TigerTag-Project/Tiger_Scale/data/www/img/bambu_grey.png

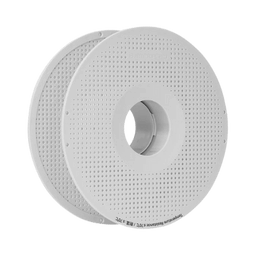
data/www/img/bambu_grey.png
