TigerTag-Project/Tiger_Scale/data/www/img/bambu_transp.png

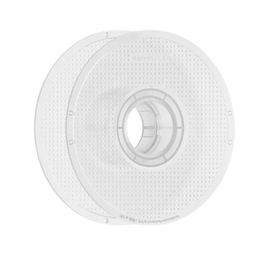
data/www/img/bambu_transp.png
