TigerTag-Project/Tiger_Scale/data/www/img/custom.png

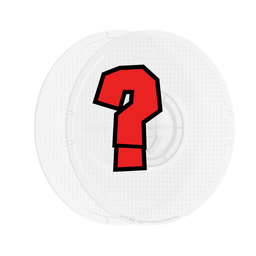
data/www/img/custom.png
