TigerTag-Project/Tiger_Scale/data/www/img/r3d_grey.png

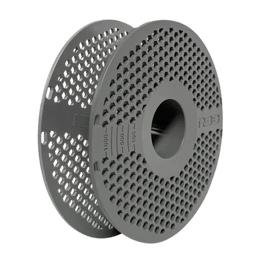
data/www/img/r3d_grey.png
