TigerTag-Project/Tiger_Scale/hardware/photo/1.jpg

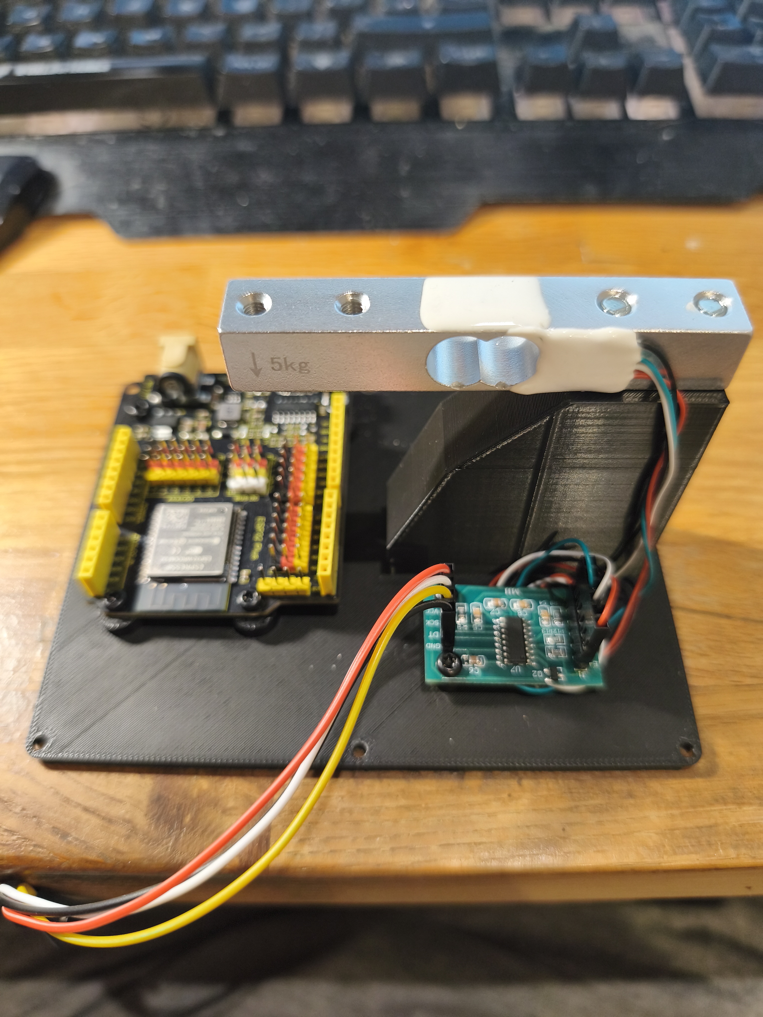
hardware/photo/1.jpg
