TigerTag-Project/Tiger_Scale/hardware/photo/2.jpg

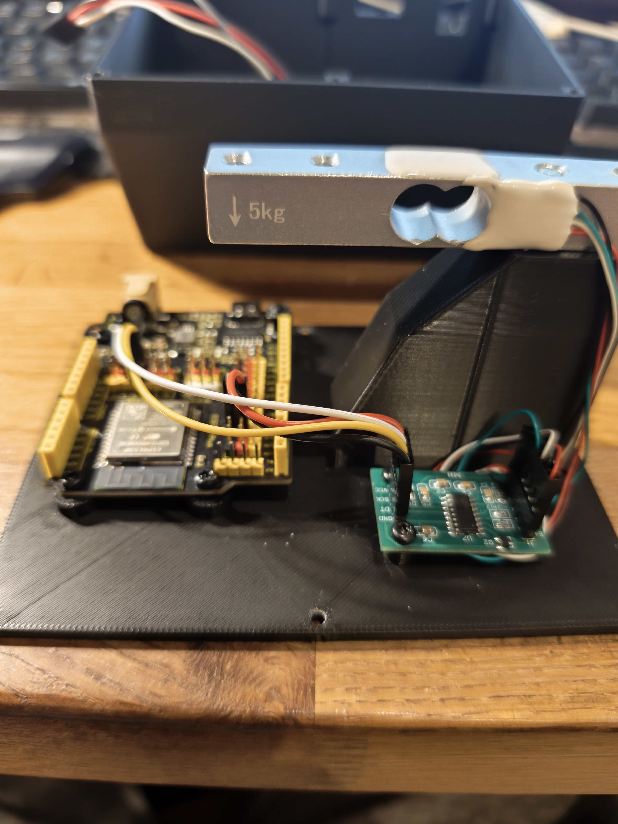
hardware/photo/2.jpg
