TigerTag-Project/Tiger_Scale/hardware/photo/3.jpg

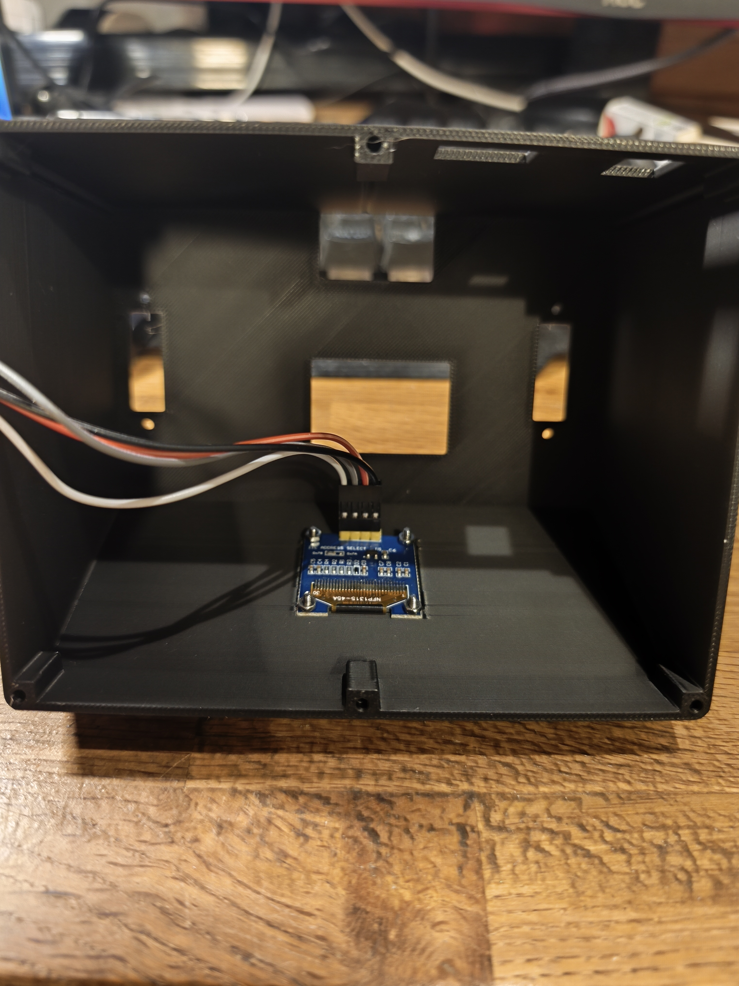
hardware/photo/3.jpg
