TigerTag-Project/Tiger_Scale/hardware/photo/4.jpg

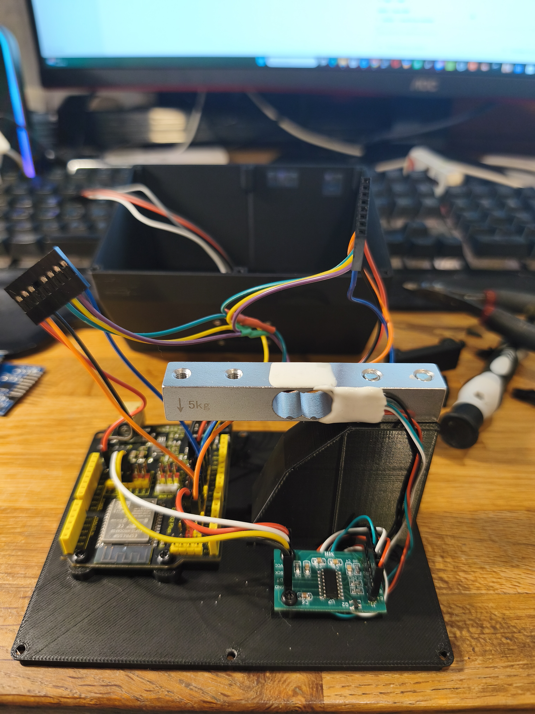
hardware/photo/4.jpg
