TigerTag-Project/Tiger_Scale/hardware/photo/6.jpg

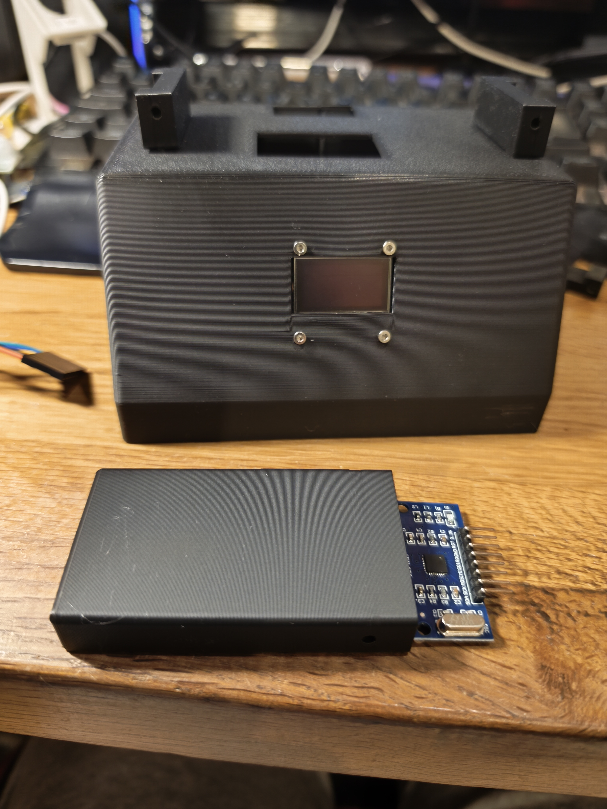
hardware/photo/6.jpg
