TigerTag-Project/Tiger_Scale/hardware/photo/8.jpg

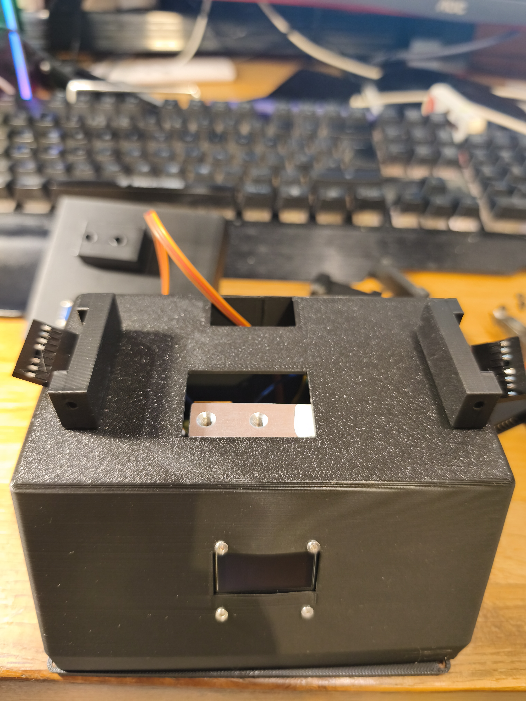
hardware/photo/8.jpg
